coolboy17289/LiPad/stl's/Main/Assembly 2 - Seeed Studio XIAO RP2040 v26 (15).stl

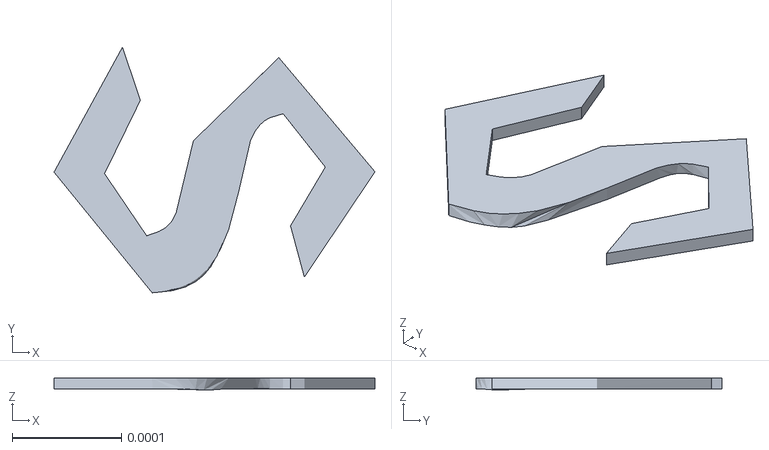
[picture p14: CAD file, 2026-07-18]
stl's/Main/Assembly 2 - Seeed Studio XIAO RP2040 v26 (15).stl
0.000293 x 0.000224 x 1.09e-05
