coolboy17289/LiPad/stl's/Main/Assembly 2 - SW_Cherry_MX_PCB_cp.stl

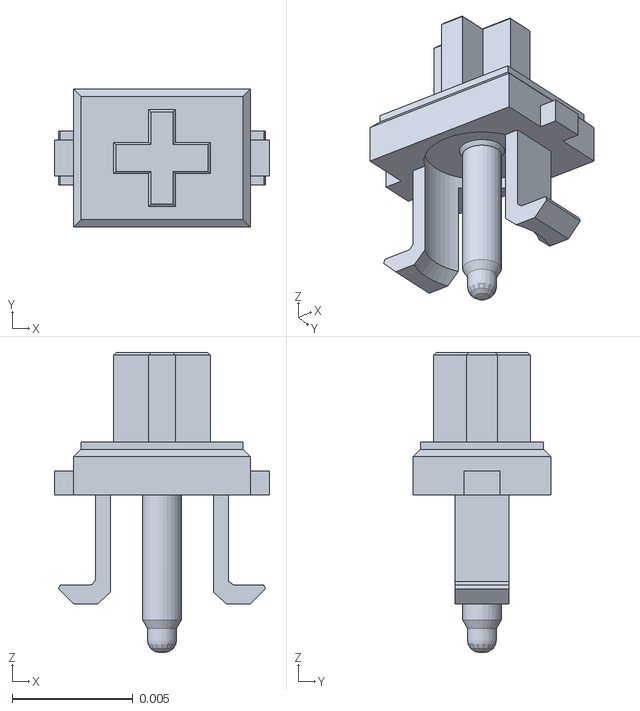
[picture p15: CAD file, 2026-07-18]
stl's/Main/Assembly 2 - SW_Cherry_MX_PCB_cp.stl
0.0089 x 0.0057 x 0.0124
