coolboy17289/LiPad/stl's/v1 do not use/Assembly 2 - Seeed Studio XIAO RP2040 v26 (61).stl

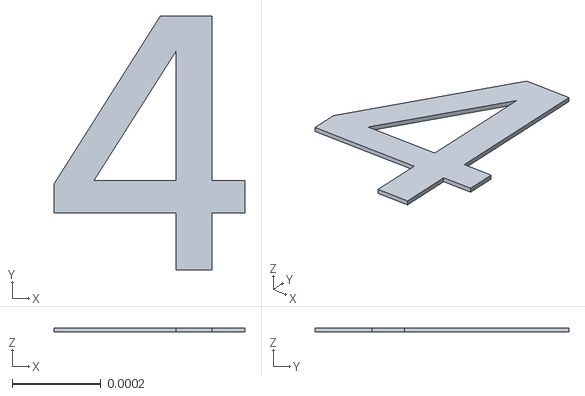
[picture p16: CAD file, 2026-07-18]
stl's/v1 do not use/Assembly 2 - Seeed Studio XIAO RP2040 v26 (61).stl
0.000429 x 0.00057 x 1e-05
