coolboy17289/LiPad/stl's/Main/Assembly 2 - Seeed Studio XIAO RP2040 v26 (79).stl

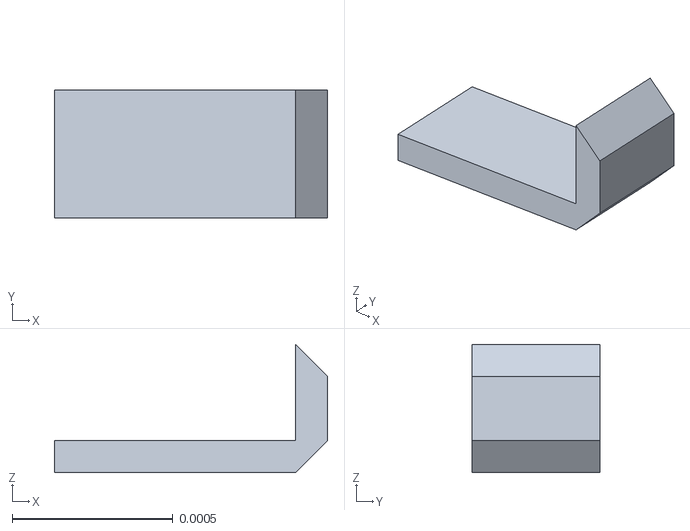
[picture p17: CAD file, 2026-07-18]
stl's/Main/Assembly 2 - Seeed Studio XIAO RP2040 v26 (79).stl
0.00085 x 0.0004 x 0.0004
