coolboy17289/LiPad/stl's/v1 do not use/Assembly 2 - Seeed Studio XIAO RP2040 v26 (50).stl

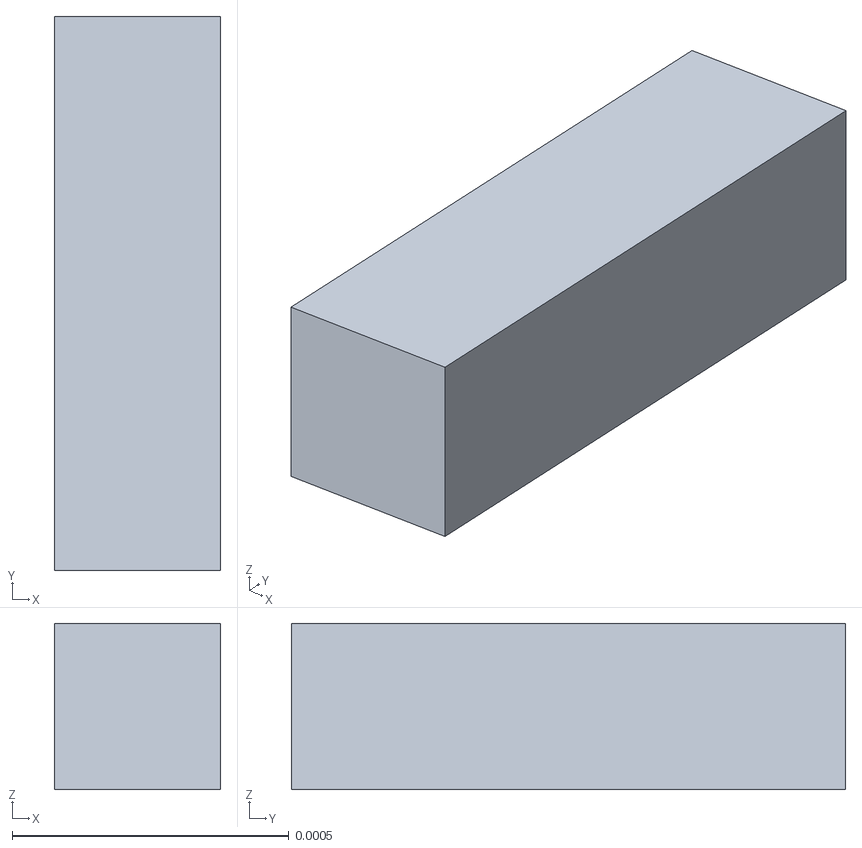
[picture p18: CAD file, 2026-07-18]
stl's/v1 do not use/Assembly 2 - Seeed Studio XIAO RP2040 v26 (50).stl
0.0003 x 0.001 x 0.0003
