coolboy17289/LiPad/stl's/Main/Assembly 2 - Pins_4.stl

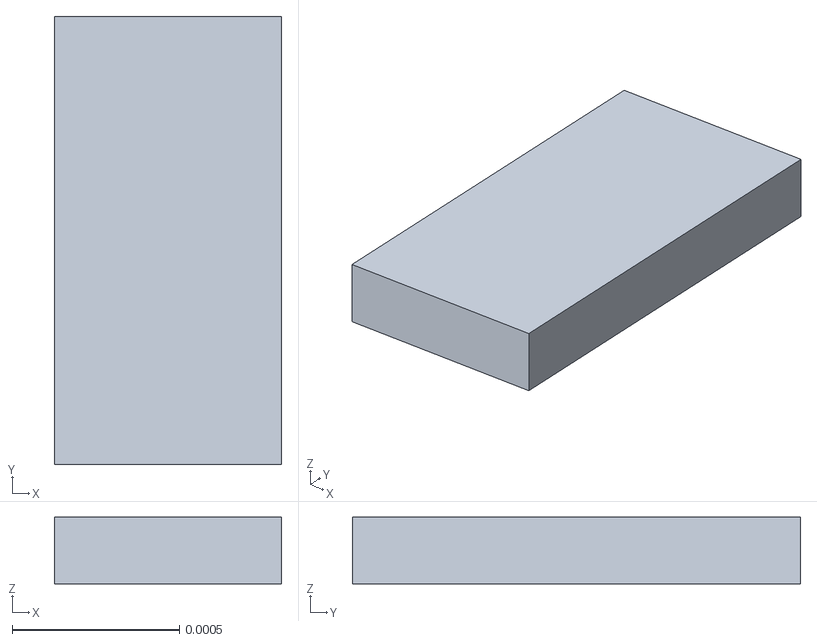
[picture p19: CAD file, 2026-07-18]
stl's/Main/Assembly 2 - Pins_4.stl
0.00068 x 0.00134 x 0.0002
