coolboy17289/LiPad/stl's/Main/Assembly 2 - Part 10.stl

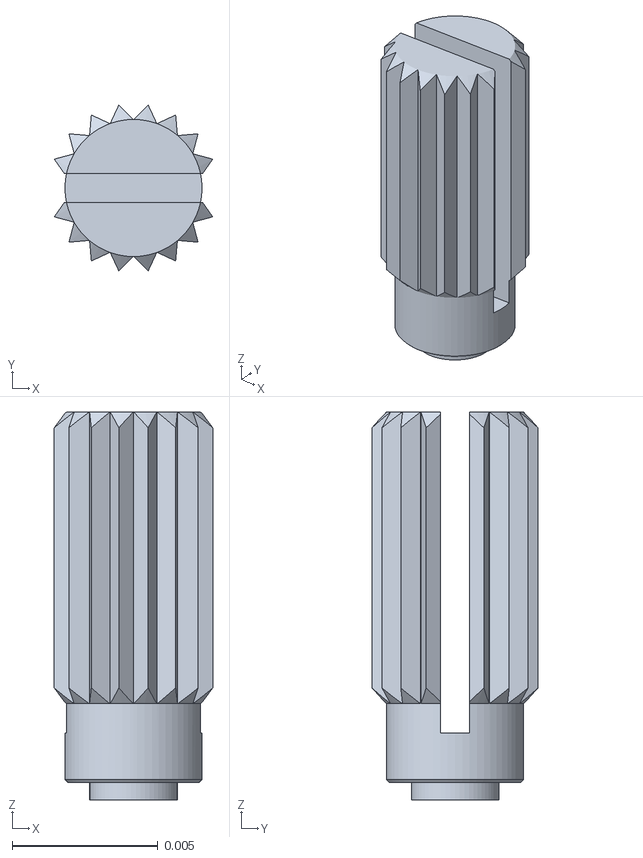
[picture p20: CAD file, 2026-07-18]
stl's/Main/Assembly 2 - Part 10.stl
0.00543 x 0.00569 x 0.0133
