coolboy17289/LiPad/stl's/v1 do not use/Assembly 2 - Seeed Studio XIAO RP2040 v26 (32).stl

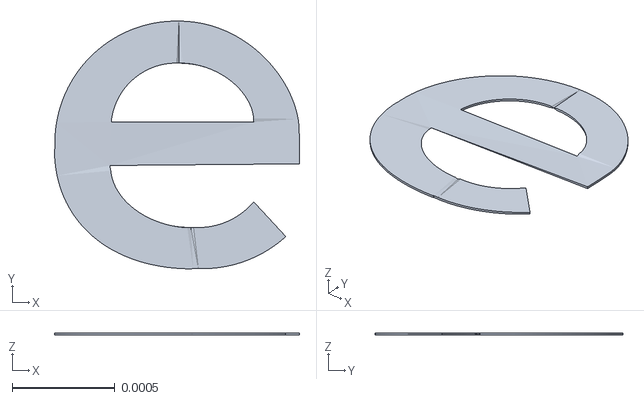
[picture p21: CAD file, 2026-07-18]
stl's/v1 do not use/Assembly 2 - Seeed Studio XIAO RP2040 v26 (32).stl
0.00119 x 0.00121 x 1e-05
