coolboy17289/LiPad/stl's/Main/Assembly 2 - Seeed Studio XIAO RP2040 v26 (49).stl

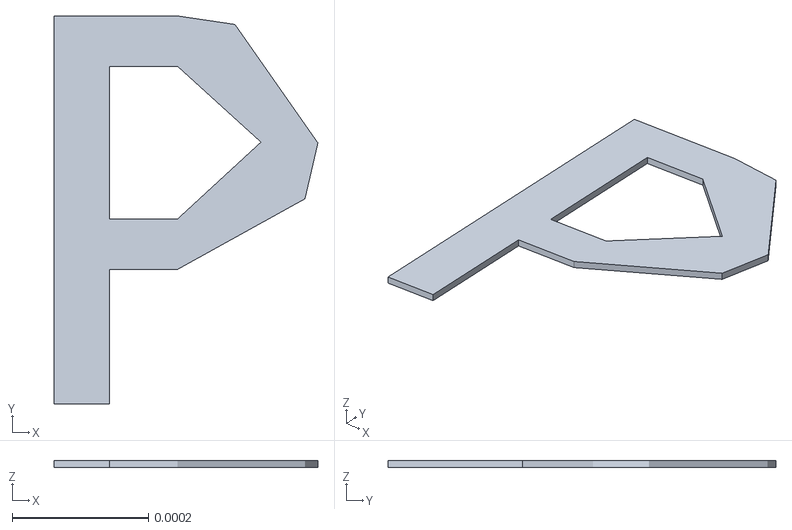
[picture p22: CAD file, 2026-07-18]
stl's/Main/Assembly 2 - Seeed Studio XIAO RP2040 v26 (49).stl
0.000388 x 0.00057 x 1e-05
