coolboy17289/LiPad/stl's/Main/Assembly 2 - Seeed Studio XIAO RP2040 v26 (47).stl

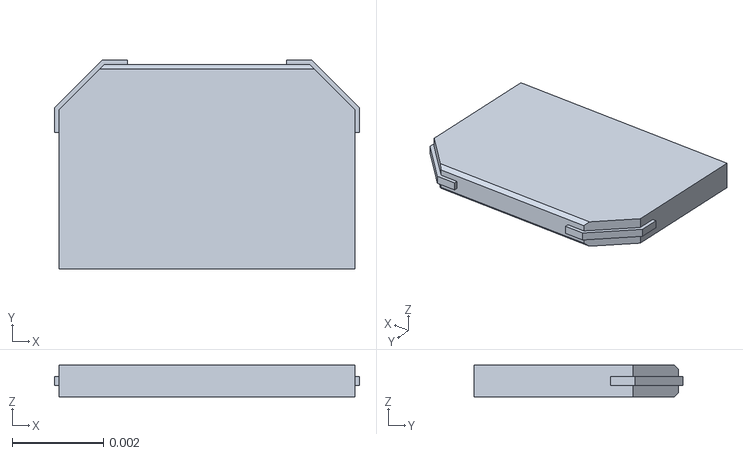
[picture p23: CAD file, 2026-07-18]
stl's/Main/Assembly 2 - Seeed Studio XIAO RP2040 v26 (47).stl
0.0067 x 0.0046 x 0.0007
