coolboy17289/LiPad/stl's/Main/Assembly 2 - Seeed Studio XIAO RP2040 v26 (17).stl

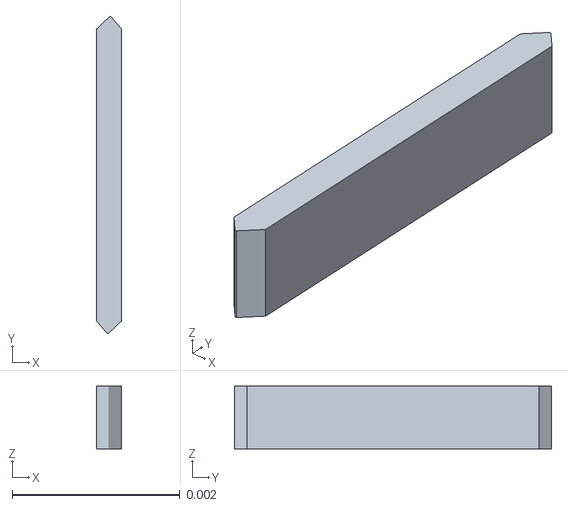
[picture p24: CAD file, 2026-07-18]
stl's/Main/Assembly 2 - Seeed Studio XIAO RP2040 v26 (17).stl
0.0003 x 0.00378 x 0.00075
