coolboy17289/LiPad/stl's/v1 do not use/Assembly 2 - SplashPad_PCB.stl

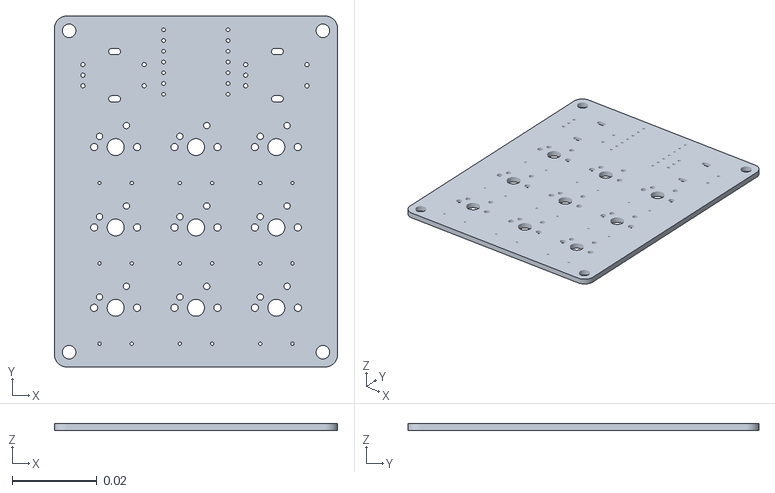
[picture p26: CAD file, 2026-07-18]
stl's/v1 do not use/Assembly 2 - SplashPad_PCB.stl
0.067 x 0.083 x 0.0016
