coolboy17289/LiPad/stl's/v1 do not use/Assembly 2 - Seeed Studio XIAO RP2040 v26 (60).stl

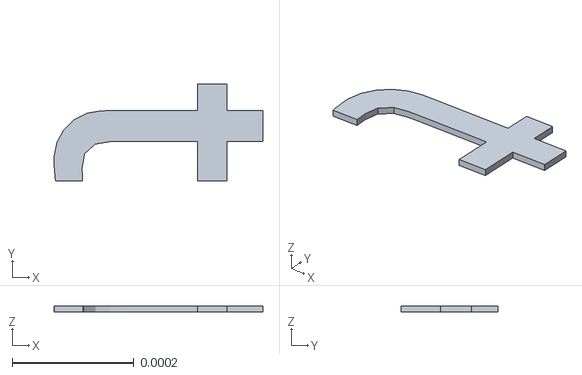
[picture p27: CAD file, 2026-07-18]
stl's/v1 do not use/Assembly 2 - Seeed Studio XIAO RP2040 v26 (60).stl
0.000343 x 0.000159 x 1e-05
