coolboy17289/LiPad/stl's/Main/Assembly 2 - Part 1.stl

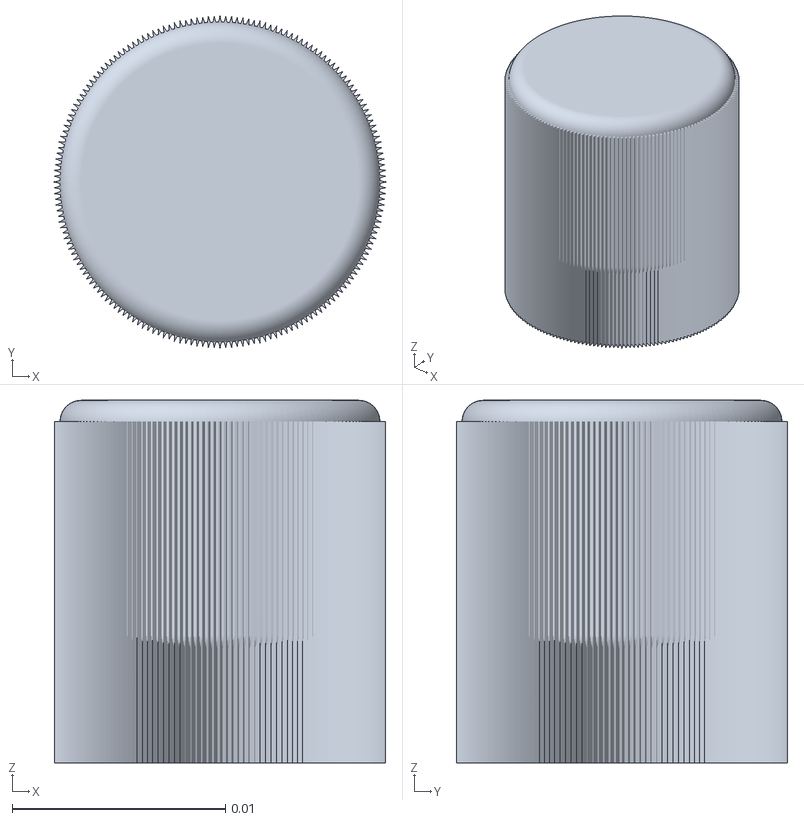
[picture p28: CAD file, 2026-07-18]
stl's/Main/Assembly 2 - Part 1.stl
0.0155 x 0.0155 x 0.017
