coolboy17289/LiPad/stl's/v1 do not use/Assembly 2 - Seeed Studio XIAO RP2040 v26 (16).stl

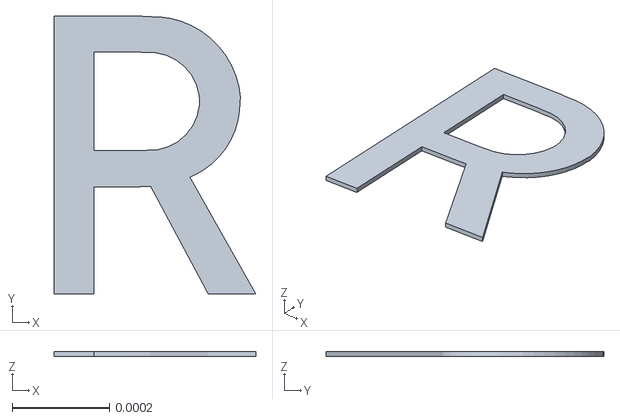
[picture p29: CAD file, 2026-07-18]
stl's/v1 do not use/Assembly 2 - Seeed Studio XIAO RP2040 v26 (16).stl
0.000414 x 0.00057 x 1e-05
