coolboy17289/LiPad/stl's/Main/Assembly 2 - Pins_7.stl

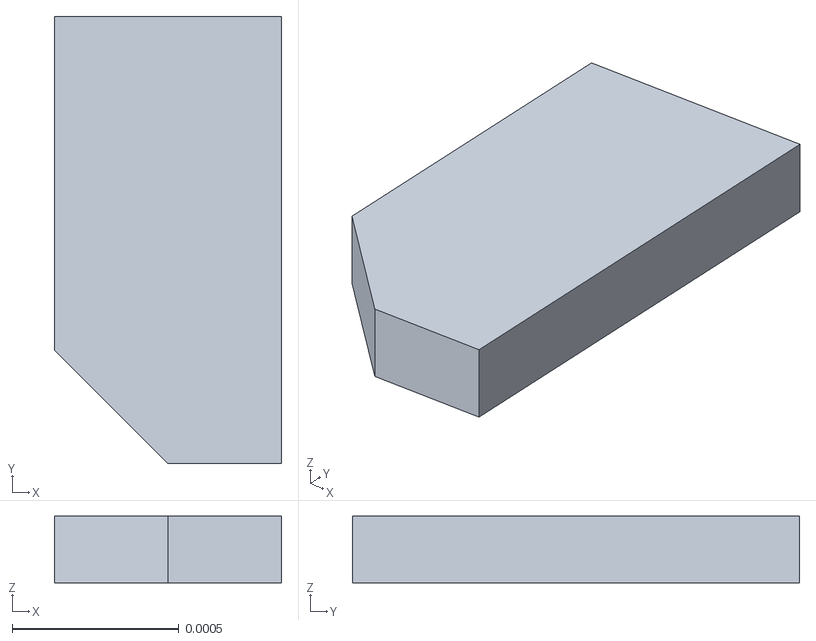
[picture p38: CAD file, 2026-07-18]
stl's/Main/Assembly 2 - Pins_7.stl
0.00068 x 0.00134 x 0.0002
