coolboy17289/LiPad/stl's/v1 do not use/Assembly 2 - Bottom Case.stl

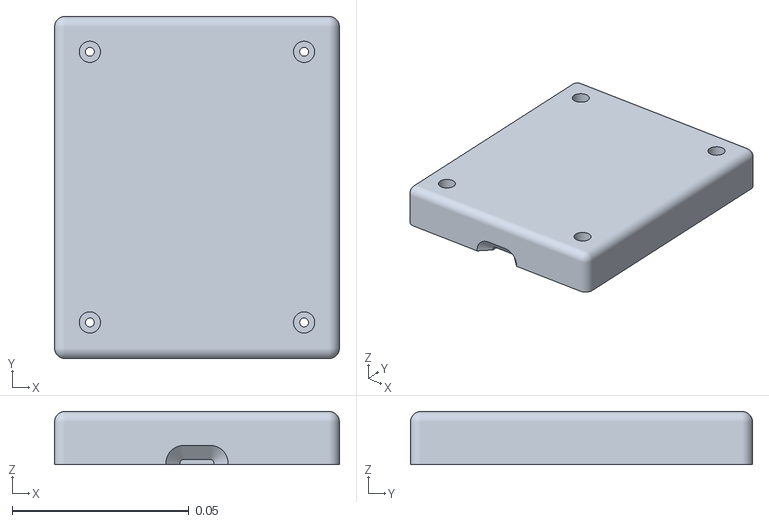
[picture p43: CAD file, 2026-07-18]
stl's/v1 do not use/Assembly 2 - Bottom Case.stl
0.0806 x 0.0967 x 0.015
