coolboy17289/LiPad/stl's/v1 do not use/Assembly 2 - Part 7.stl

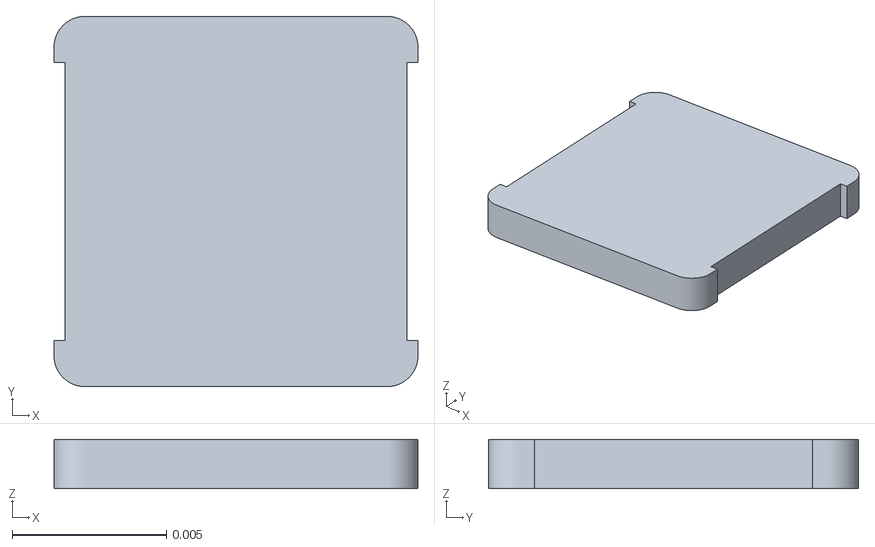
[picture p46: CAD file, 2026-07-18]
stl's/v1 do not use/Assembly 2 - Part 7.stl
0.0118 x 0.012 x 0.0016
