coolboy17289/LiPad/stl's/v1 do not use/Assembly 2 - SW_Cherry_MX_PCB_cp_5.stl

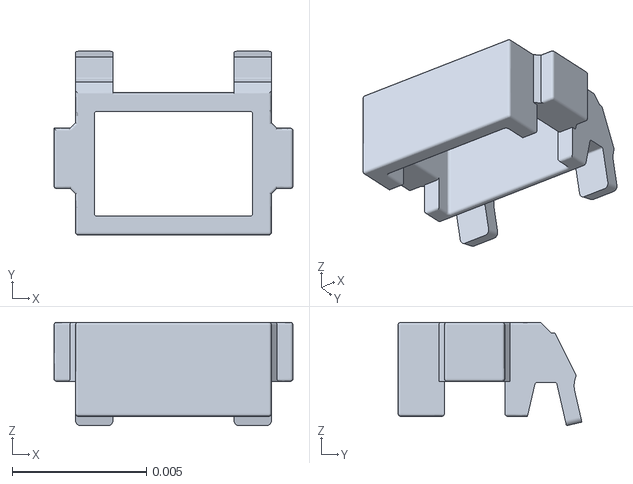
[picture p52: CAD file, 2026-07-18]
stl's/v1 do not use/Assembly 2 - SW_Cherry_MX_PCB_cp_5.stl
0.0089 x 0.00685 x 0.00385
