coolboy17289/LiPad/stl's/v1 do not use/Assembly 2 - SW_Cherry_MX_PCB_cp_6 (4).stl

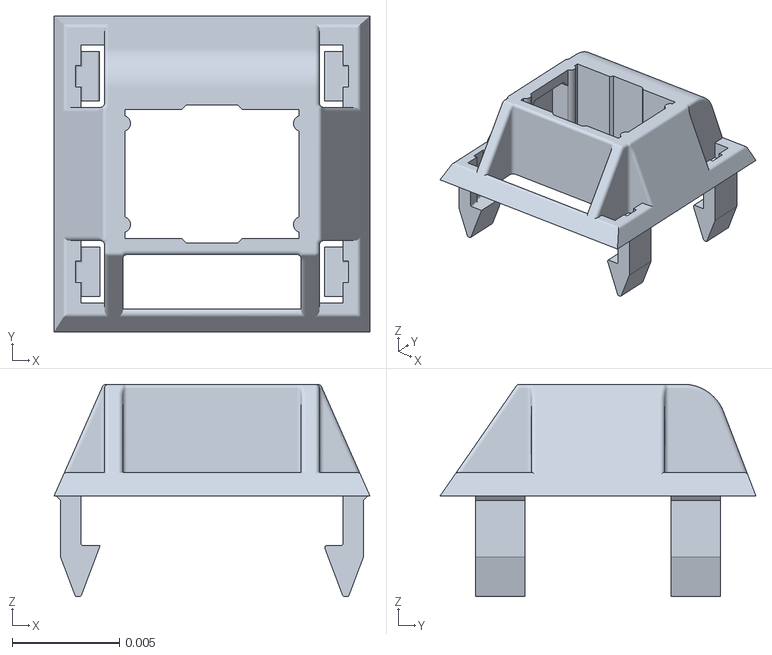
[picture p54: CAD file, 2026-07-18]
stl's/v1 do not use/Assembly 2 - SW_Cherry_MX_PCB_cp_6 (4).stl
0.0147 x 0.0147 x 0.00989
