coolboy17289/LiPad/stl's/Main/Assembly 2 - top cover.stl

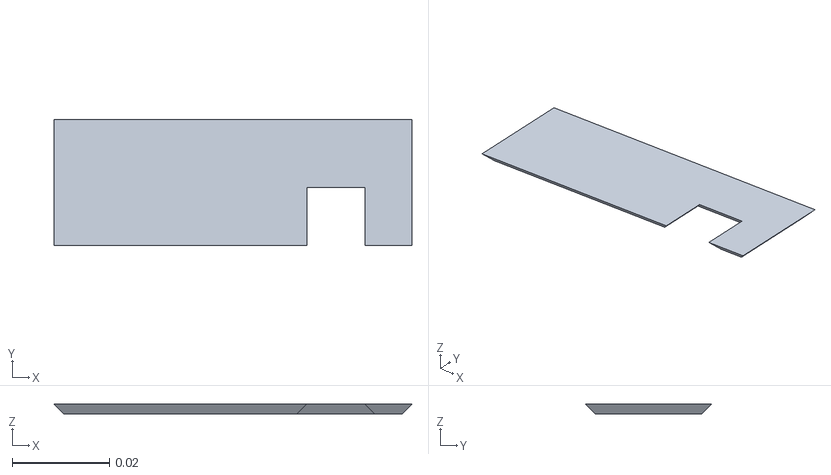
[picture p57: CAD file, 2026-07-18]
stl's/Main/Assembly 2 - top cover.stl
0.0737 x 0.026 x 0.002
