coolboy17289/LiPad/stl's/v1 do not use/Assembly 2 - Part 9.stl

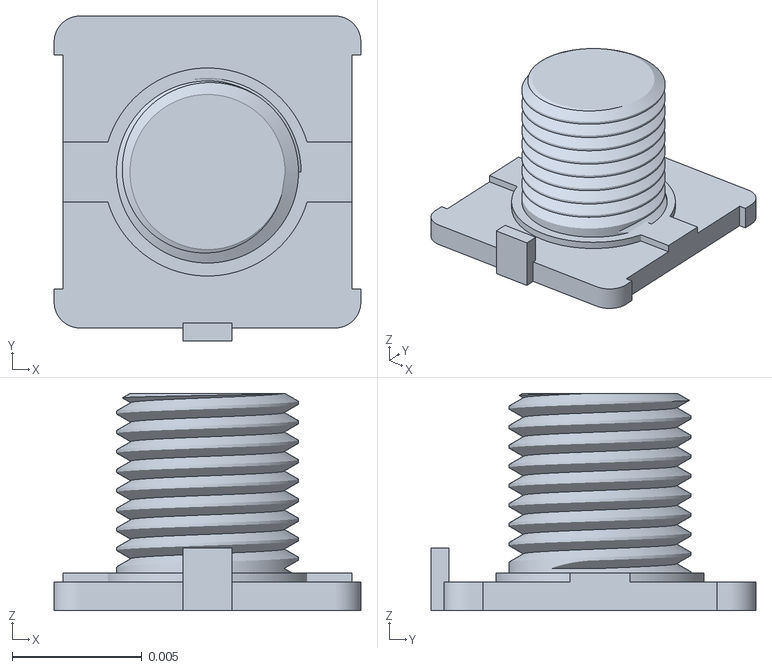
[picture p58: CAD file, 2026-07-18]
stl's/v1 do not use/Assembly 2 - Part 9.stl
0.0118 x 0.0125 x 0.00835
